felixkuebler/HomeAutomation-LightSwitch/Hardware/Electronics/Render/LightSwitch_bottom.jpg

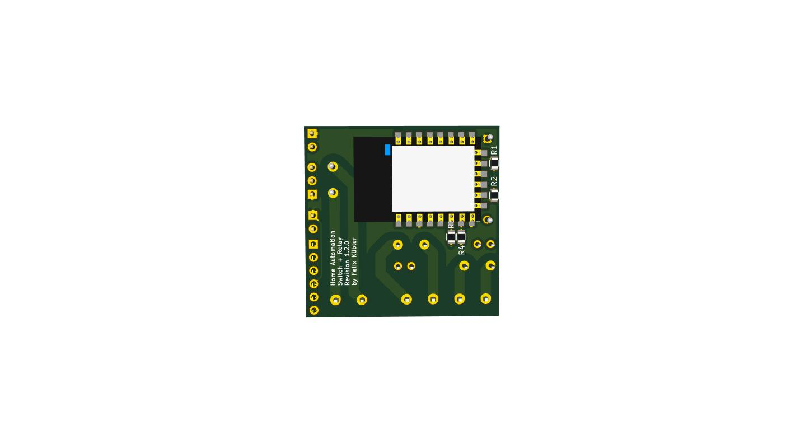
Hardware/Electronics/Render/LightSwitch_bottom.jpg
