felixkuebler/HomeAutomation-LightSwitch/Hardware/Mechanics/Render/LightSwitch_Bottom.jpg

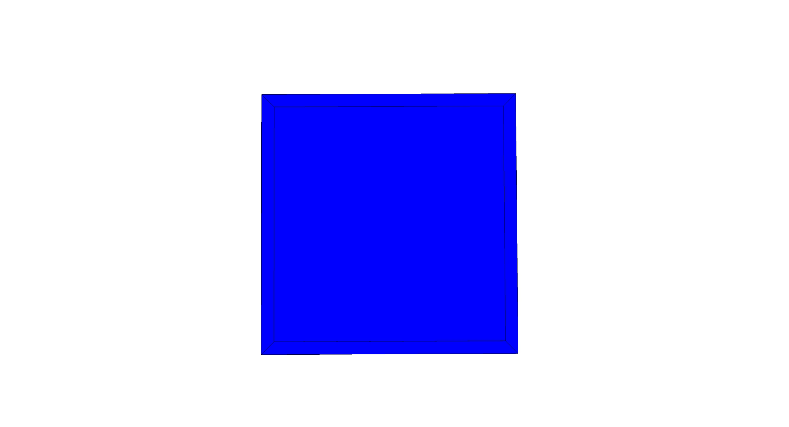
Hardware/Mechanics/Render/LightSwitch_Bottom.jpg
